drkmsmithjr/ETANixieClock/SimCalcFiles/Nixie_Driver.asc

Q1: npn; 2N5550
Q2: pnp; 2N5401
Q3: pnp; 2N5401
Q4: npn; 2N5550
R1: res; 470k
R2: res; 10k
R3: res; 10k
R4: res; 10k
R5: res; 470k
R6: res; 22k
R7: res; 100k
R8: res; 470k
R9: res; 470k
R10: res; 100k
V1: voltage; 140
V2: voltage; 5
V3: voltage; PULSE(5 0 10u 10n 10n 200u 400u)
Named nets: 0
.tran 20m
